moonbeaminteractive/polearm-weapon/Design/Screen Shot 2016-12-15 at 12.27.21 PM.png

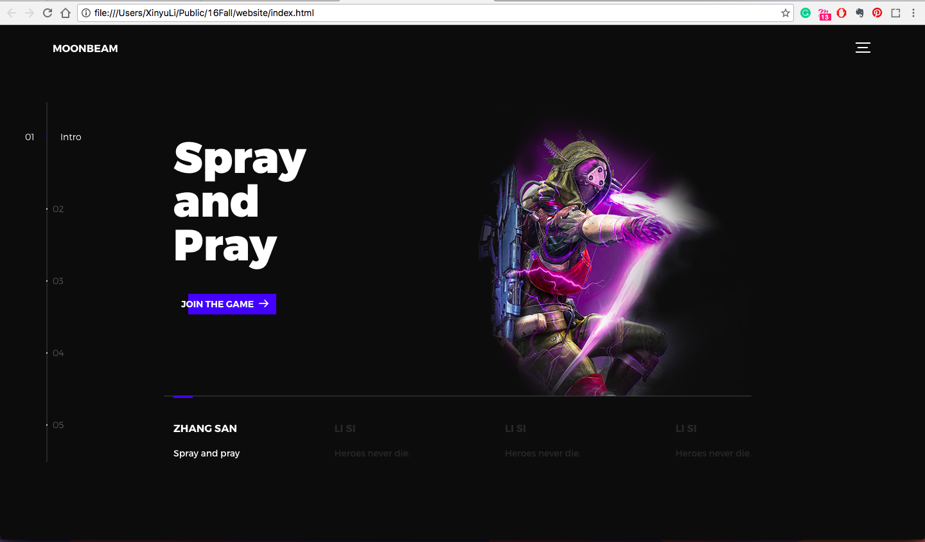
Design/Screen Shot 2016-12-15 at 12.27.21 PM.png
