moonbeaminteractive/polearm-weapon/hardware/rod-layout-1.jpg

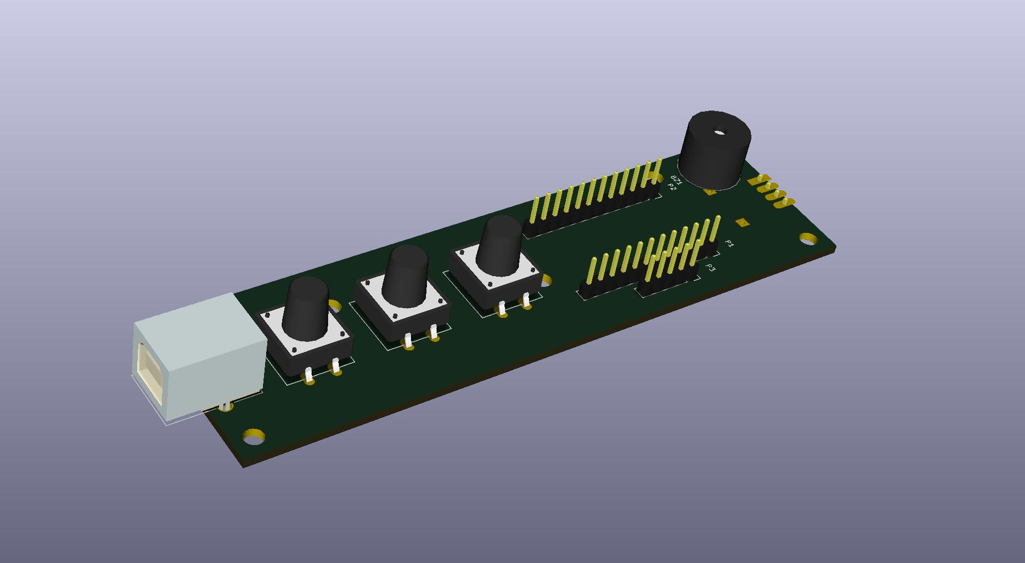
hardware/rod-layout-1.jpg
