moonbeaminteractive/polearm-weapon/hardware/rod_back.png

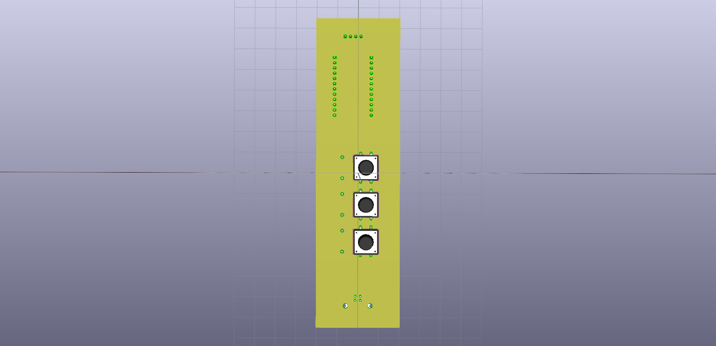
hardware/rod_back.png
