moonbeaminteractive/polearm-weapon/rod_gyro.png

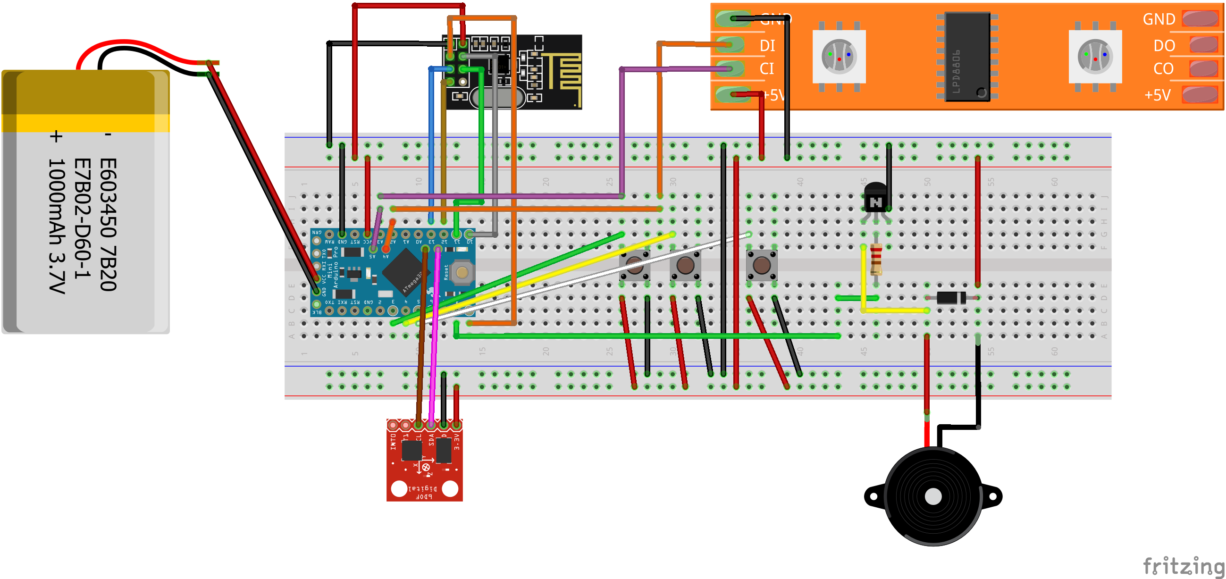
rod_gyro.png
